armanilab/MAP/CAD/MAP_STEP_files/Led_Cover.step

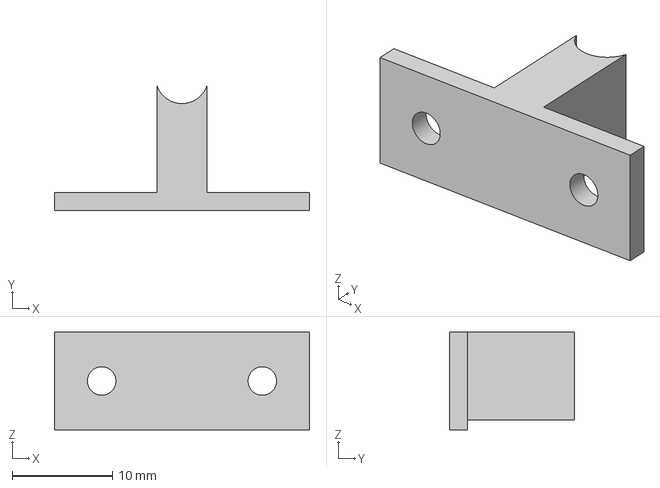
[picture p16: CAD file, 2023-04-03]
CAD/MAP_STEP_files/Led_Cover.step
25.4 x 12.5 x 9.75 mm
