armanilab/MAP/CAD/STL/magnet_spacer_1-4_v1.stl

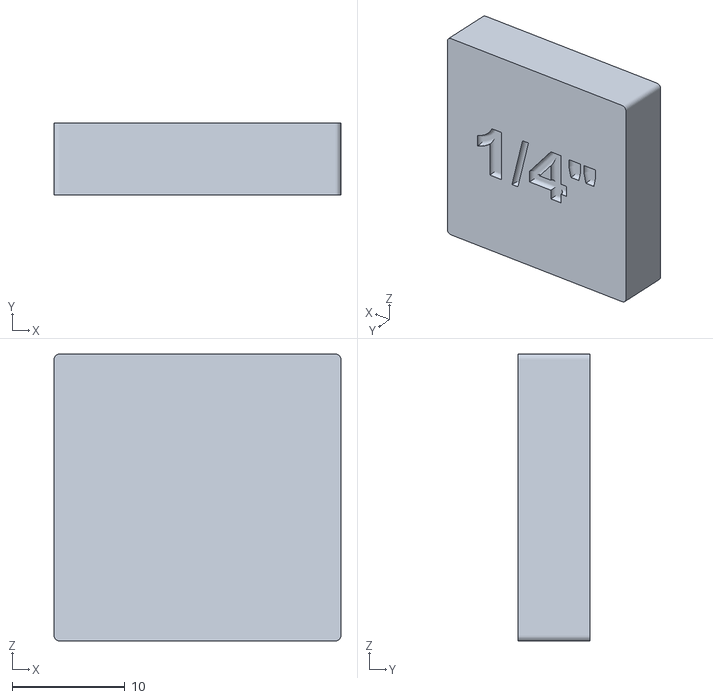
[picture p17: CAD file, 2025-03-04]
CAD/STL/magnet_spacer_1-4_v1.stl
25.4 x 6.35 x 25.4
