armanilab/MAP/CAD/stl_files/magnet_storage_latch.stl

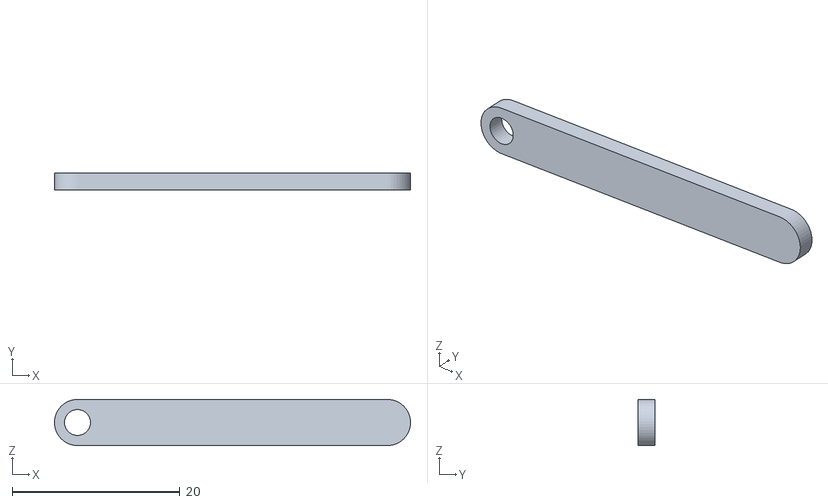
[picture p18: CAD file, 2023-04-03]
CAD/stl_files/magnet_storage_latch.stl
42.5 x 2.00 x 5.50
