armanilab/MAP/CAD/STL/magnet_storage_drawer_v1.stl

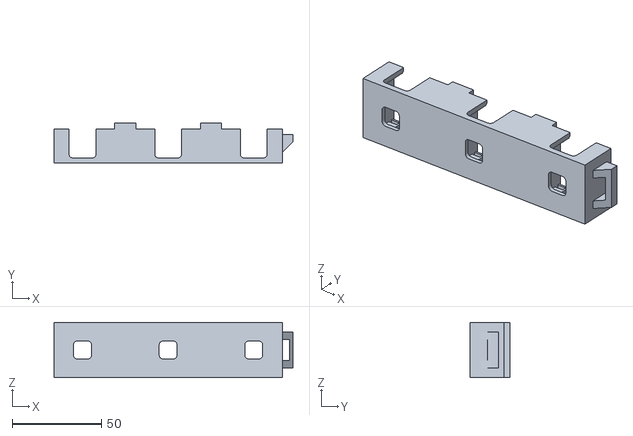
[picture p19: CAD file, 2025-03-04]
CAD/STL/magnet_storage_drawer_v1.stl
134.0 x 22.7 x 31.0
