armanilab/MAP/CAD/MAP_STEP_files/Magnet_Slider.step

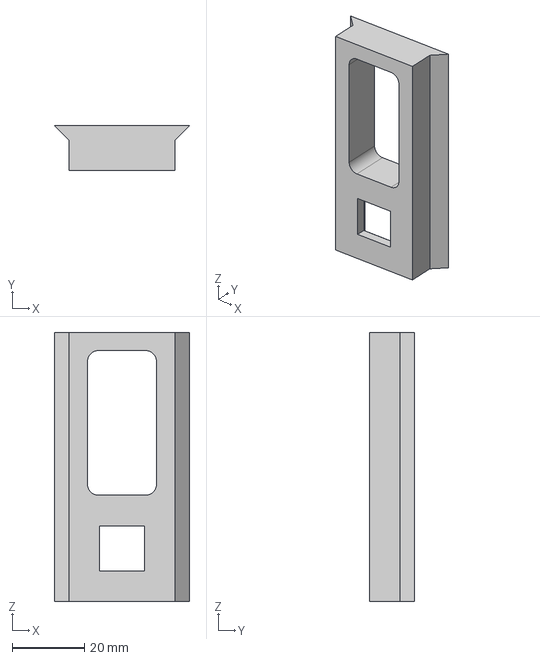
[picture p20: CAD file, 2023-04-03]
CAD/MAP_STEP_files/Magnet_Slider.step
37.4 x 12.5 x 74.4 mm
