armanilab/MAP/CAD/STL/sensor_pinhole_v1.stl

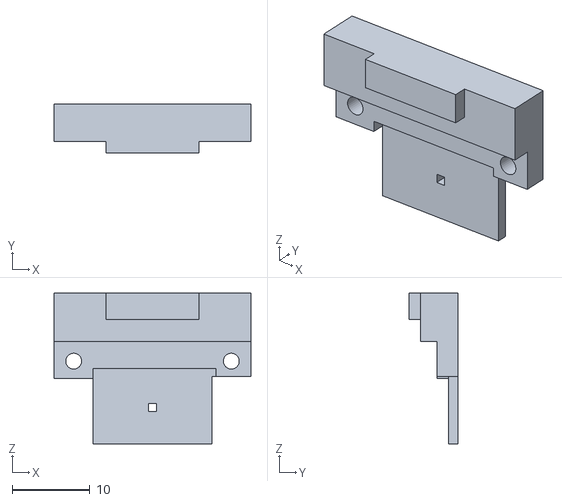
[picture p21: CAD file, 2025-03-04]
CAD/STL/sensor_pinhole_v1.stl
25.4 x 6.30 x 19.4
