armanilab/MAP/CAD/STL/led_cover_v1.stl

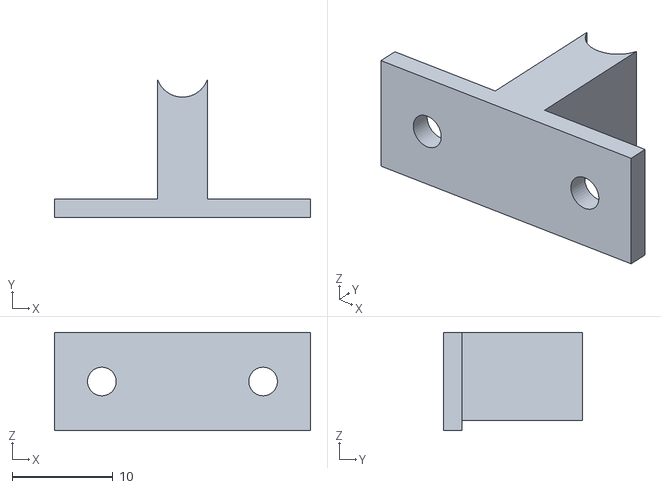
[picture p22: CAD file, 2025-03-04]
CAD/STL/led_cover_v1.stl
25.4 x 13.7 x 9.75
