armanilab/MAP/code/hardware_tests/sensor_test_v2/sensor_test_v2.ino

/* Modified from Adafruit's TSL2591 Library example script tsl2591.ino
 * for use with the MAP hardware
 *    By: Lexie Scholtz
 *    Created: 2023.06.14
 *    Last updated: 2023.06.14
 */

/* TSL2591 Digital Light Sensor */
/* Dynamic Range: 600M:1 */
/* Maximum Lux: 88K */

#include <Wire.h>
#include <Adafruit_Sensor.h>
#include "Adafruit_TSL2591.h"

// Example for demonstrating the TSL2591 library - public domain!

// connect SCL to I2C Clock
// connect SDA to I2C Data
// connect Vin to 3.3-5V DC
// connect GROUND to common ground

Adafruit_TSL2591 tsl = Adafruit_TSL2591(2591); // pass in a number for the sensor identifier (for your use later)


/**************************************************************************/
/*
    Configures the gain and integration time for the TSL2591
*/
/**************************************************************************/
void configureSensor(void)
{
  // You can change the gain on the fly, to adapt to brighter/dimmer light situations
  tsl.setGain(TSL2591_GAIN_LOW);    // 1x gain (bright light)
  
  // Changing the integration time gives you a longer time over which to sense light
  // longer timelines are slower, but are good in very low light situtations!
  tsl.setTiming(TSL2591_INTEGRATIONTIME_100MS);  // shortest integration time (bright light)

  /* Display the gain and integration time for reference sake */  
  Serial.println(F("------------------------------------"));
  Serial.print  (F("Gain:         "));
  tsl2591Gain_t gain = tsl.getGain();
  Serial.println(F("1x (Low)"));
  
  Serial.print  (F("Timing:       "));
  Serial.print((tsl.getTiming() + 1) * 100, DEC); 
  Serial.println(F(" ms"));
  Serial.println(F("------------------------------------"));
  Serial.println(F(""));
}


/**************************************************************************/
/*
    Program entry point for the Arduino sketch
*/
/**************************************************************************/
void setup(void) 
{
  Serial.begin(9600);

  // for the Feather - which takes an extra step to properly setup the Serial code
  if (!Serial) {
    delay(10);
  }
  delay(500);
  
  Serial.println(F("Starting Adafruit TSL2591 Test!"));
  
  if (tsl.begin()) 
  {
    Serial.println(F("Found a TSL2591 sensor"));
  } 
  else 
  {
    Serial.println(F("No sensor found ... check your wiring?"));
    while (1);
  }
    
  /* Display some basic information on this sensor */
  displaySensorDetails();
  
  /* Configure the sensor */
  configureSensor();

  // Now we're ready to get readings ... move on to loop()!
}


/**************************************************************************/
/*
    Show how to read IR and Full Spectrum at once and convert to lux
*/
/**************************************************************************/
void advancedRead(void)
{
  // More advanced data read example. Read 32 bits with top 16 bits IR, bottom 16 bits full spectrum
  // That way you can do whatever math and comparisons you want!
  uint32_t lum = tsl.getFullLuminosity();
  uint16_t ir, full;
  ir = lum >> 16;
  full = lum & 0xFFFF;
  Serial.print(F("Lux: ")); Serial.println(tsl.calculateLux(full, ir), 6);
}

/**************************************************************************/
/*
    Arduino loop function, called once 'setup' is complete (your own code
    should go here)
*/
/**************************************************************************/
void loop(void) 
{ 
  //simpleRead(); 
  advancedRead();
  // unifiedSensorAPIRead();
  
  delay(500);
}
