armanilab/MAP/code/hardware_tests/change_button_i2c/change_button_i2c.ino

/*
 * Code for MAP hardware tests.
 * Allows to change button I2C address
 * Script modified from Sparkfun provided example
 * Written by: Lexie Scholtz
 * Created: 2022.09.29
 * Last Updated: 2023.04.03
*/

/*
 * Make sure you only connect the green Qwiic button to the Feather! 
 * All other I2C devices must be disconnected.
*/

#include <SparkFun_Qwiic_Button.h>
QwiicButton button;

void setup() {
  Serial.begin(115200);

  while (!Serial) { // wait for Serial port to open
    delay(10);
  }
  delay(500);

  Wire.begin(); //Join I2C bus

  if (button.begin() == false) {
    Serial.println("Device did not acknowledge! Running scanner.");
  }
  else{
    Serial.println("Device acknowledged!");
  
    Serial.println();
    Serial.println("Enter a new I2C address for the Qwiic Button/Switch to use!");
    Serial.println("Don't use the 0x prefix. For instance, if you wanted to");
    Serial.println("change the address to 0x5B, you would enter 5B and press enter.");
    Serial.println();
    Serial.println("One more thing! Make sure your line ending is set to 'Both NL & CR'");
    Serial.println("in the Serial Monitor.");
    Serial.println();

    //Wait for serial data to be available
    while (Serial.available() == 0);
  
    if (Serial.available()) {
      uint8_t newAddress = 0;
      String stringBuffer = Serial.readString();
      char charBuffer[10];
      stringBuffer.toCharArray(charBuffer, 10);
      uint8_t success = sscanf(charBuffer, "%x", &newAddress);
  
      if (success) {
        if (newAddress > 0x08 && newAddress < 0x77) {
          Serial.println("Character recieved, and device address is valid!");
          Serial.print("Attempting to set device address to 0x");
          Serial.println(newAddress, HEX);
  
          if (button.setI2Caddress(newAddress) == true) {
            Serial.println("Device address set succeeded!");
          }
  
          else {
            Serial.println("Device address set failed!");
          }
  
          delay(100); //give the hardware time to do whatever configuration it needs to do
  
          if (button.isConnected()) {
            Serial.println("Device will acknowledge on new I2C address!");
          }
  
          else {
            Serial.println("Device will not acknowledge on new I2C address.");
          }
        }
  
        else {
          Serial.println("Address out of range! Try an address between 0x08 and 0x77");
        }
      }
  
      else {
        Serial.print("Invalid Text! Try again.");
      }
    }
    delay(100);
  }


}

void loop() {
  //if no I2C device found or Qwiic button correctly set to new address, 
  //scan for available I2C devices
  byte error, address;
  int nDevices;

  Serial.println("Scanning...");

  nDevices = 0;
  for (address = 1; address < 127; address++ )
  {
    // The i2c_scanner uses the return value of
    // the Write.endTransmisstion to see if
    // a device did acknowledge to the address.
    Wire.beginTransmission(address);
    error = Wire.endTransmission();

    if (error == 0)
    {
      Serial.print("I2C device found at address 0x");
      if (address < 16)
        Serial.print("0");
      Serial.print(address, HEX);
      Serial.println("  !");

      nDevices++;
    }
    else if (error == 4)
    {
      Serial.print("Unknown error at address 0x");
      if (address < 16)
        Serial.print("0");
      Serial.println(address, HEX);
    }
  }
  if (nDevices == 0)
    Serial.println("No I2C devices found\n");
  else
    Serial.println("done\n");

  delay(10000);           // wait 10 seconds for next scan

}
